jludwig75/led_light_contoller/src/altfadefunc.h

#include "fadefunc.h"


class AlternateFadeFunction : public FadeFunction
{
public:
    AlternateFadeFunction(unsigned long offTime, unsigned long fadeTime, unsigned long onTime);
    StripeValues operator()(unsigned long time) override;
private:
    int activeStripe(unsigned long time);
};
